CheeseCube312/CCubes-Filter-holding-Adapter/Konica AR/CAD/Fitler Holder/Holder - 33x3mm filter.step

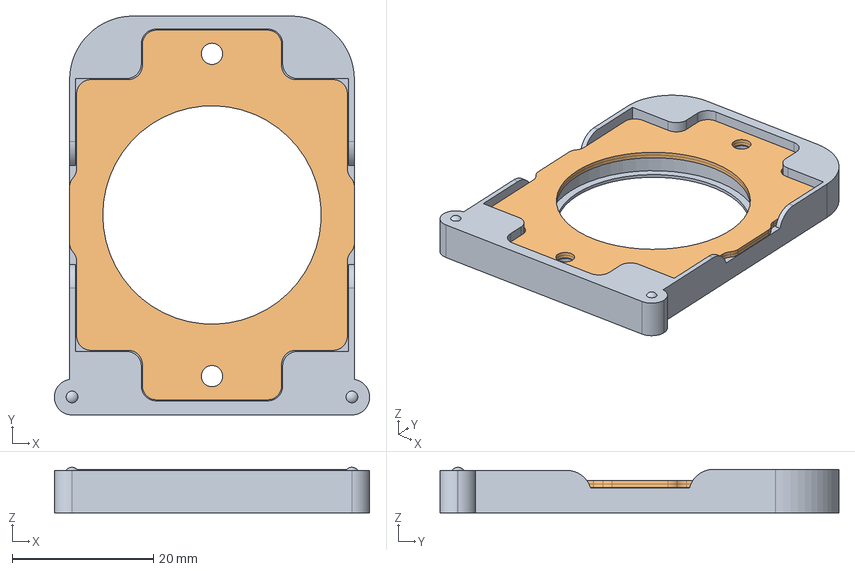
[picture p17: CAD file, 2025-07-29]
Konica AR/CAD/Fitler Holder/Holder - 33x3mm filter.step
44.6 x 56.5 x 6.45 mm
