CheeseCube312/CCubes-Filter-holding-Adapter/Konica AR/Print/Filter Holder/Holder - 36x1mm filter.3mf

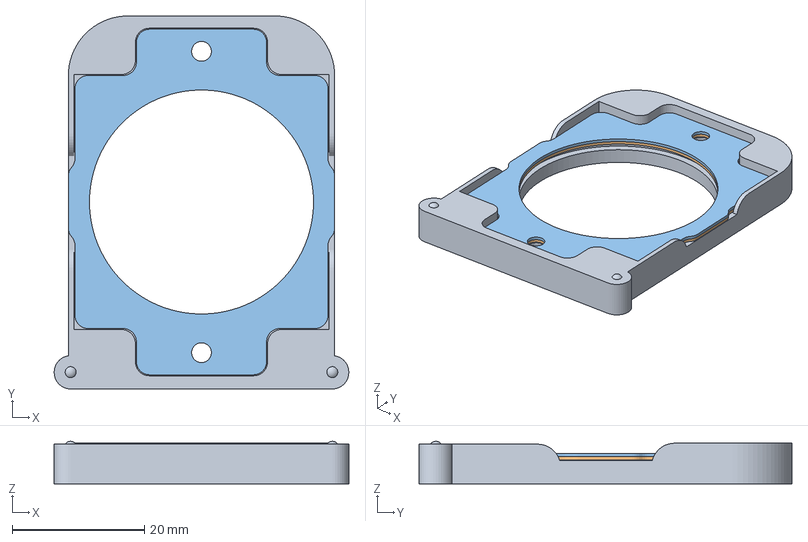
[picture p24: CAD file, 2025-07-29]
Konica AR/Print/Filter Holder/Holder - 36x1mm filter.3mf
44.6 x 56.5 x 6.45 mm
Filter Holder Body
Holder Plate Glass
Holder Plate Normal
